DragonRoyal/stasis-hxthm/cad/Stepper motor 28BYJ-48 5V.SLDPRT

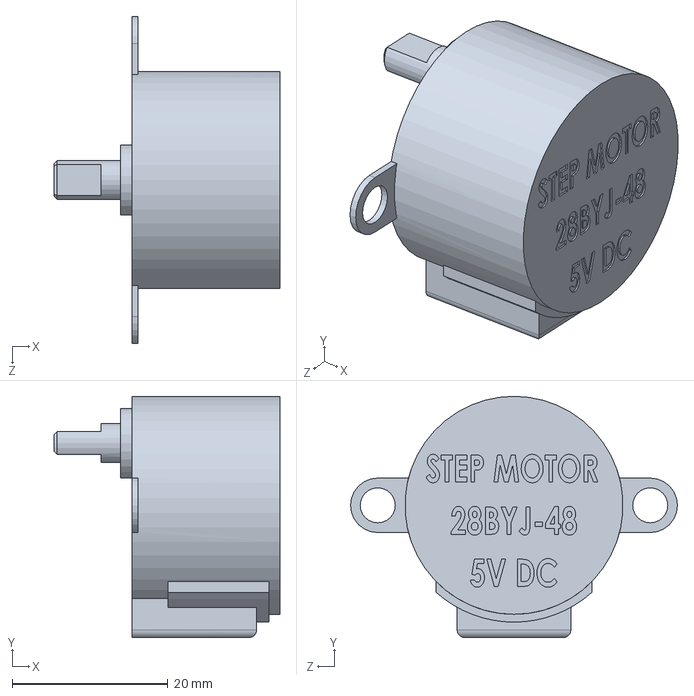
[picture p15: CAD file, 2026-05-16]
cad/Stepper motor 28BYJ-48 5V.SLDPRT
29.0 x 31.0 x 42.0 mm
